dudgeon/agent-ptt-mic/hardware/mockup/output/renders/exploded_iso.png

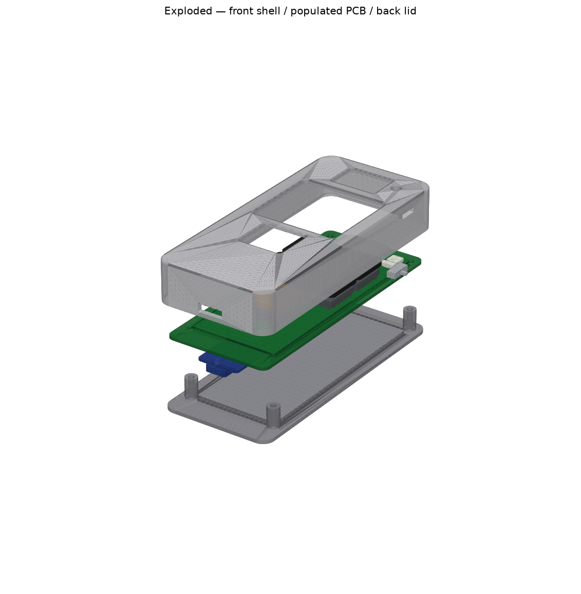
hardware/mockup/output/renders/exploded_iso.png
