dudgeon/agent-ptt-mic/hardware/mockup/output/renders/front_ortho.png

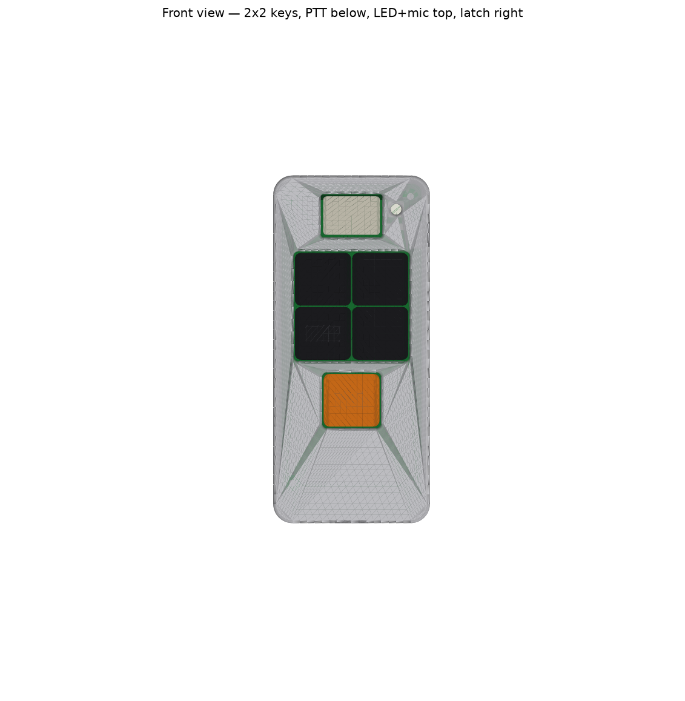
hardware/mockup/output/renders/front_ortho.png
