dudgeon/agent-ptt-mic/hardware/mockup/output/renders/internals_iso.png

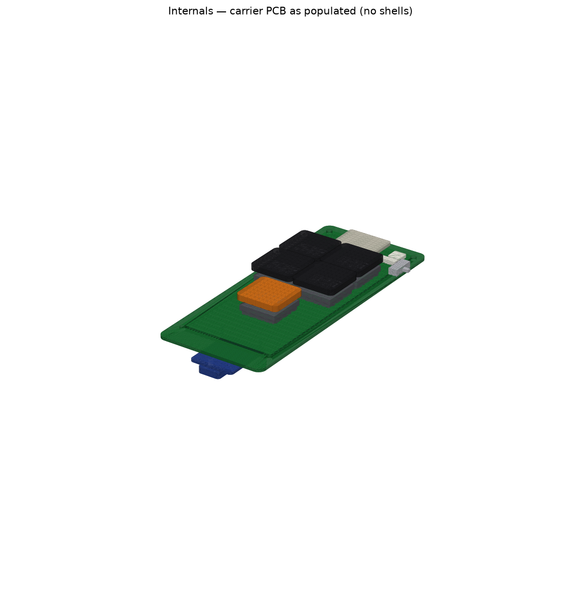
hardware/mockup/output/renders/internals_iso.png
