dudgeon/agent-ptt-mic/hardware/mockup/output/renders/internals_rear_iso.png

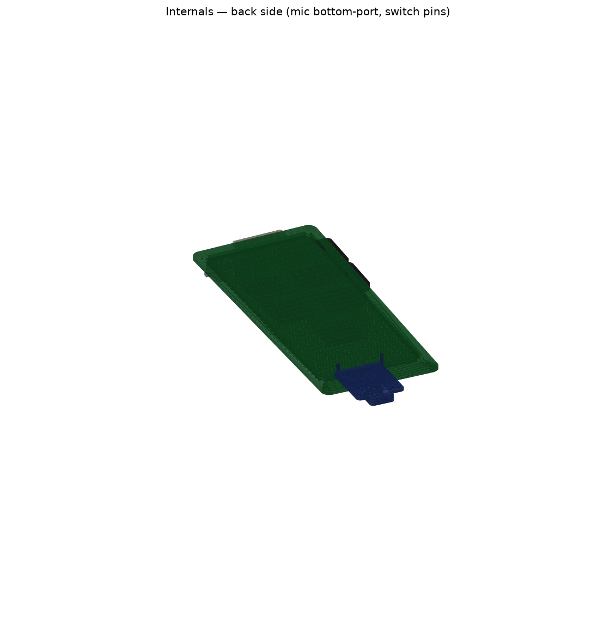
hardware/mockup/output/renders/internals_rear_iso.png
