dudgeon/agent-ptt-mic/hardware/mockup/output/renders/led_detail_front.png

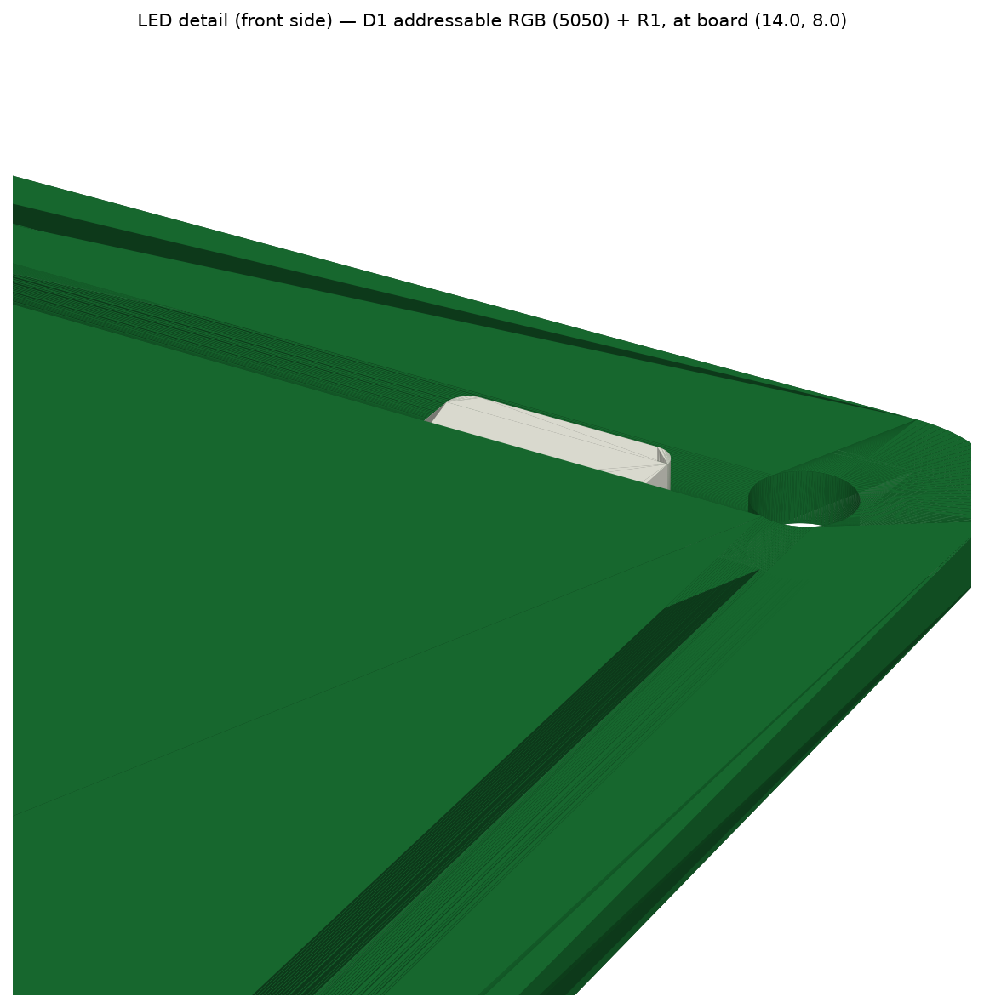
hardware/mockup/output/renders/led_detail_front.png
