dudgeon/agent-ptt-mic/hardware/mockup/output/renders/mic_detail_front.png

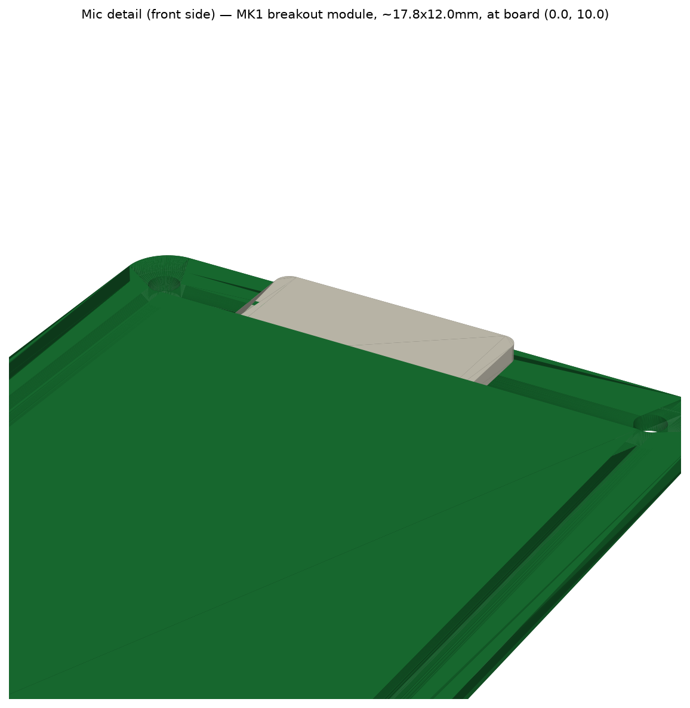
hardware/mockup/output/renders/mic_detail_front.png
