dudgeon/agent-ptt-mic/hardware/mockup/output/renders/assembled_rear_iso.png

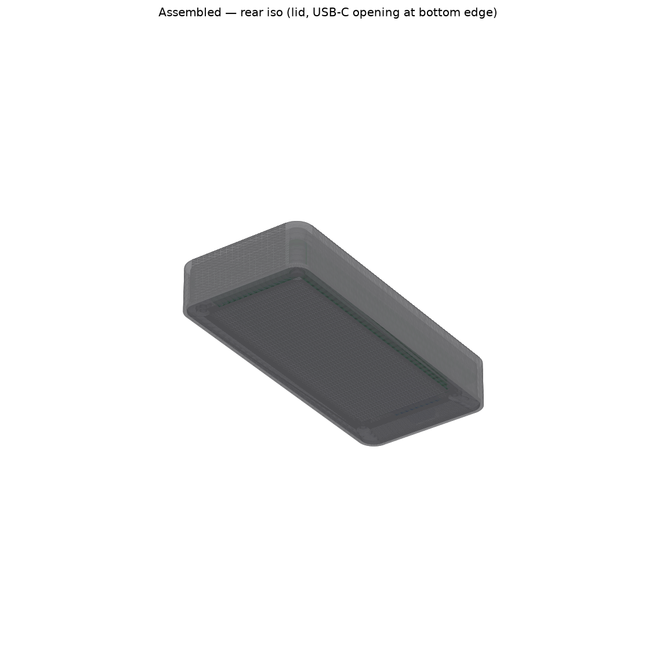
hardware/mockup/output/renders/assembled_rear_iso.png
